PoyntingPro/WifiAudioLink_Hardware/resources/schmatic.png

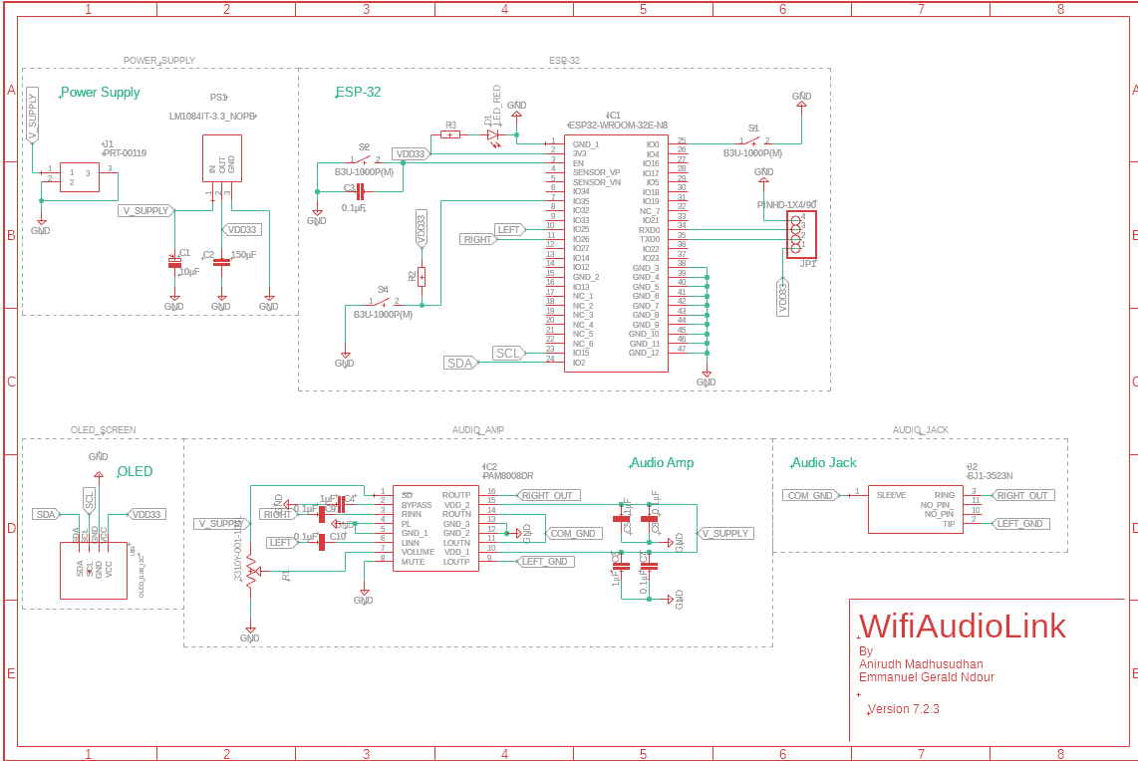
resources/schmatic.png
